leolochte/18650_UPS/Screenshots/2020-3226.jpg

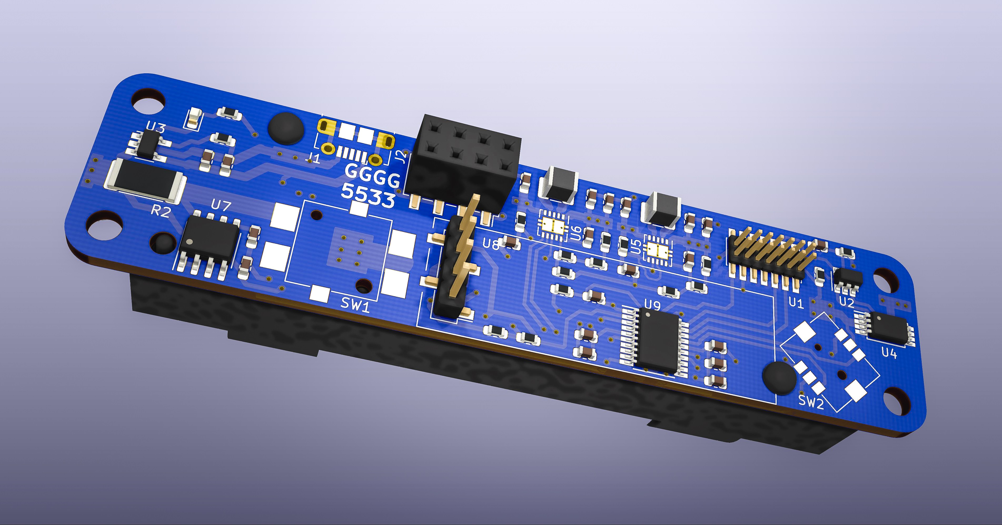
Screenshots/2020-3226.jpg
